nemocazin/stm32f030f4-bare-metal-programming/PCB/SparkFun-KiCad-Libraries-master/Documentation/Graphics Work/Symbols_raw.png

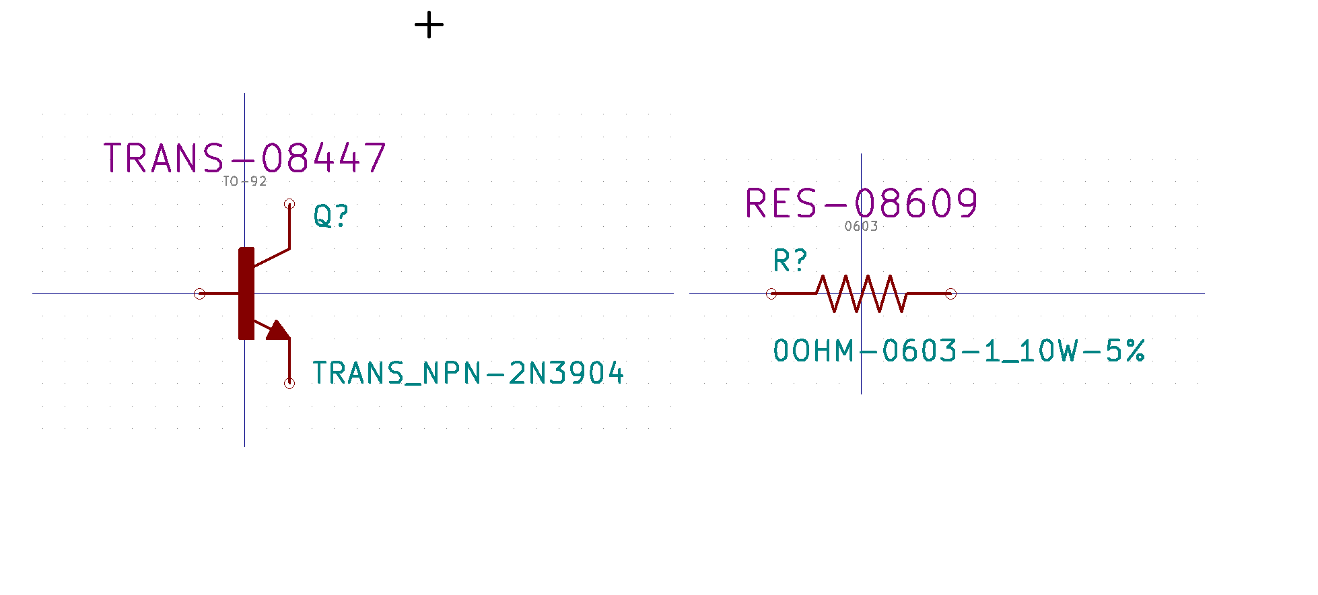
PCB/SparkFun-KiCad-Libraries-master/Documentation/Graphics Work/Symbols_raw.png
