nemocazin/stm32f030f4-bare-metal-programming/PCB/SparkFun-KiCad-Libraries-master/Tools/SparkFun-Eagle-Libraries_Conversion/description_tag_example.jpg

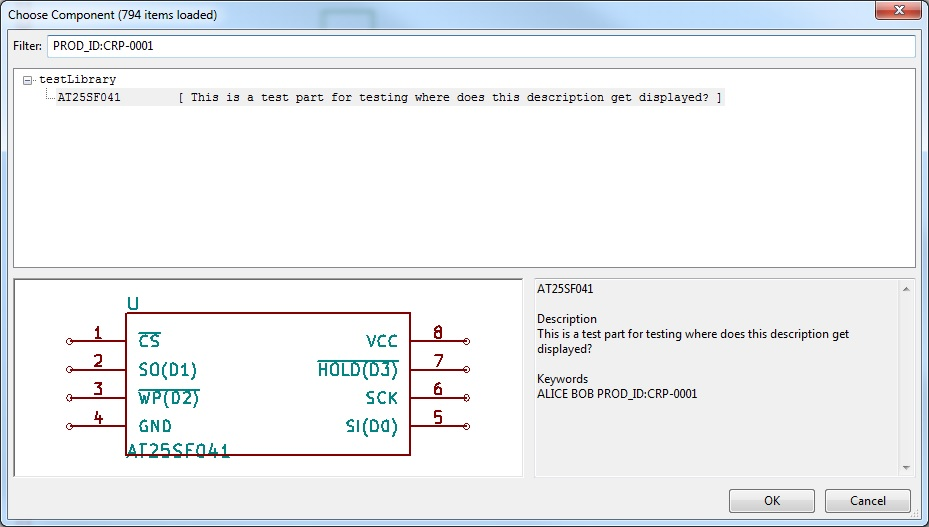
PCB/SparkFun-KiCad-Libraries-master/Tools/SparkFun-Eagle-Libraries_Conversion/description_tag_example.jpg
