nemocazin/stm32f030f4-bare-metal-programming/PCB/SparkFun-KiCad-Libraries-master/Tools/SparkFun-Eagle-Libraries_Conversion/example5.jpg

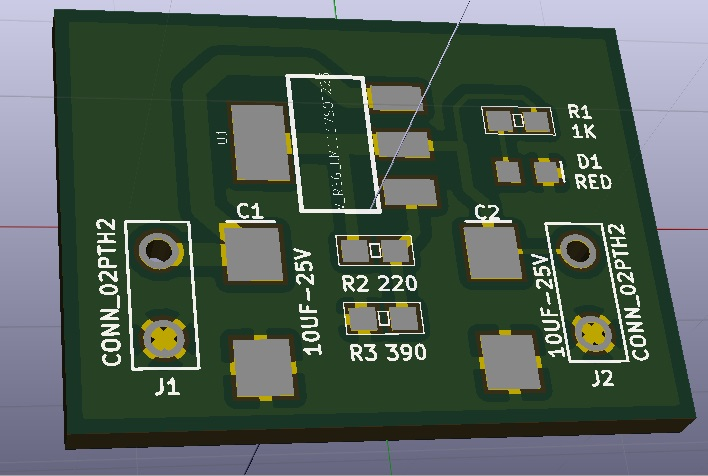
PCB/SparkFun-KiCad-Libraries-master/Tools/SparkFun-Eagle-Libraries_Conversion/example5.jpg
