nemocazin/stm32f030f4-bare-metal-programming/PCB/SparkFun-KiCad-Libraries-master/Documentation/Pictures/SymbolGuidelines.png

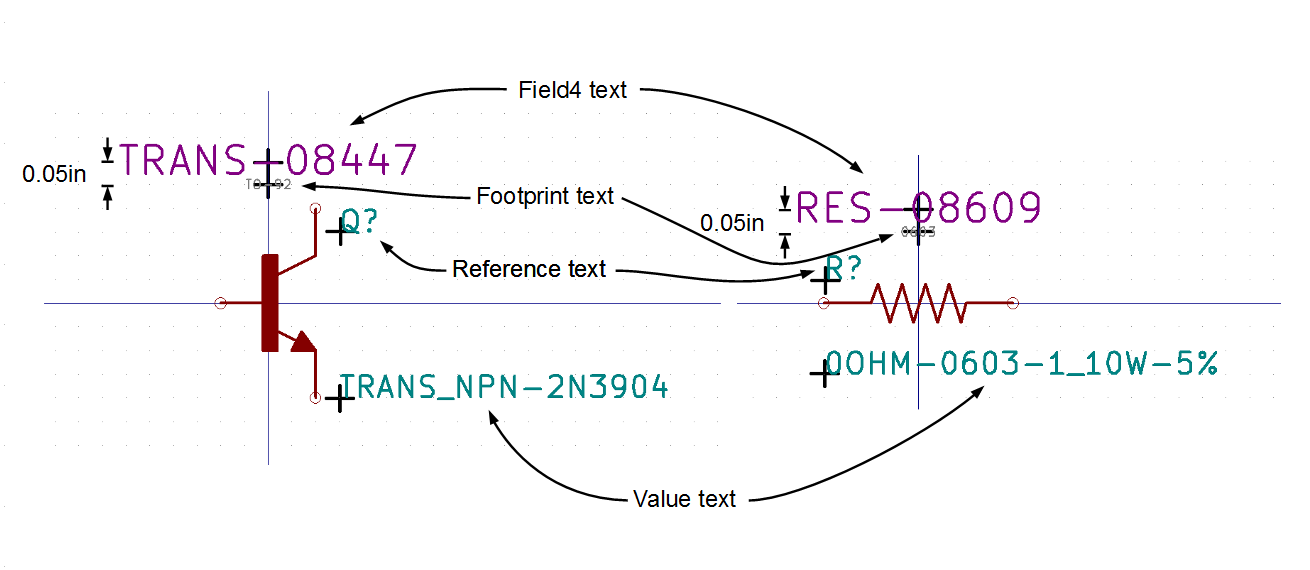
PCB/SparkFun-KiCad-Libraries-master/Documentation/Pictures/SymbolGuidelines.png
